fescrb/gc_shoulder_button/parts/lip/lip.scad

module lip() {
    cube([3,9,1]);
    translate([0,0,1]){
        cube([1,9,0.5]);
    }
}
lip();
